kblomqvist/cativity/sw/nrf51/documentation/s110/html/app_fifo_initialized.png

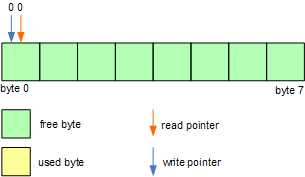
sw/nrf51/documentation/s110/html/app_fifo_initialized.png
