kblomqvist/cativity/sw/nrf51/documentation/s110/html/app_gpiote_01.png

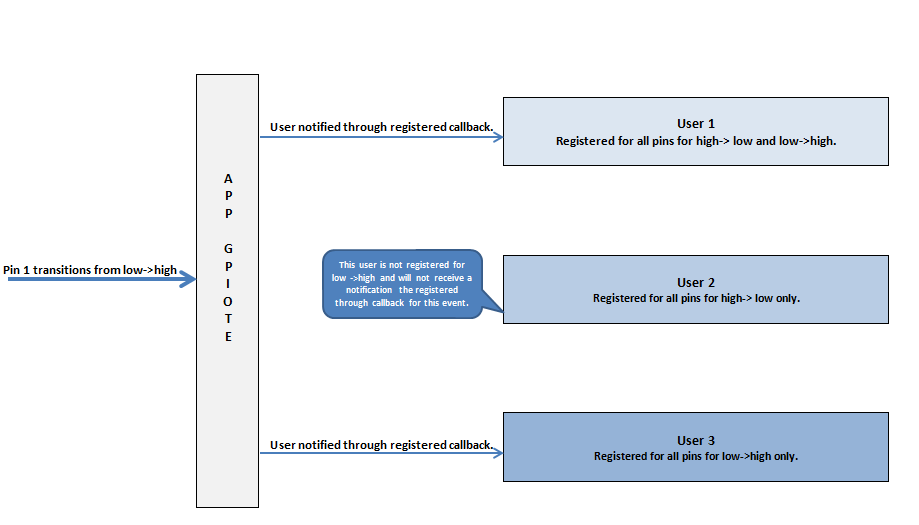
sw/nrf51/documentation/s110/html/app_gpiote_01.png
