kblomqvist/cativity/sw/nrf51/documentation/s110/html/battery_timer_without_scheduler.jpg

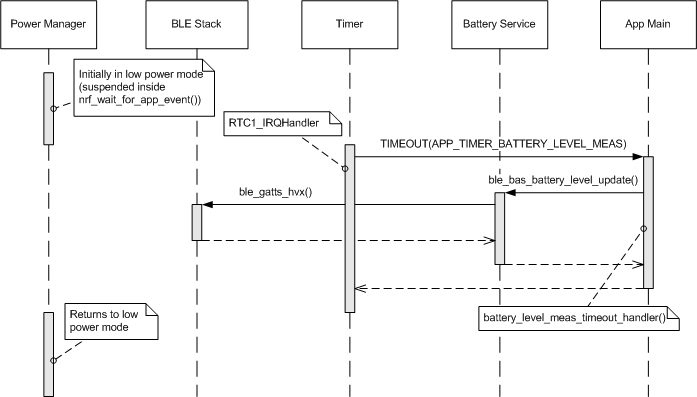
sw/nrf51/documentation/s110/html/battery_timer_without_scheduler.jpg
