kblomqvist/cativity/sw/nrf51/documentation/s110/html/ble_event_without_scheduler.jpg

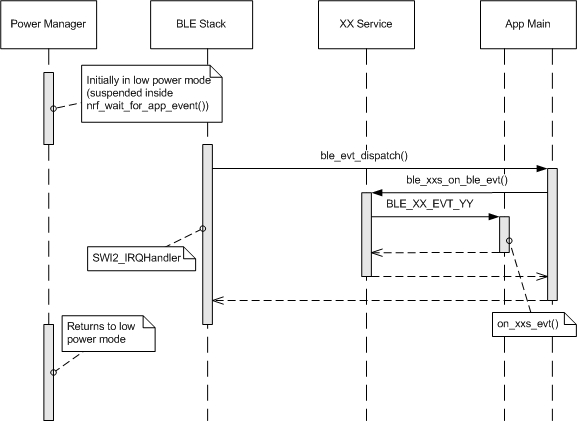
sw/nrf51/documentation/s110/html/ble_event_without_scheduler.jpg
