kblomqvist/cativity/sw/nrf51/documentation/s110/html/blinky_rtx.jpg

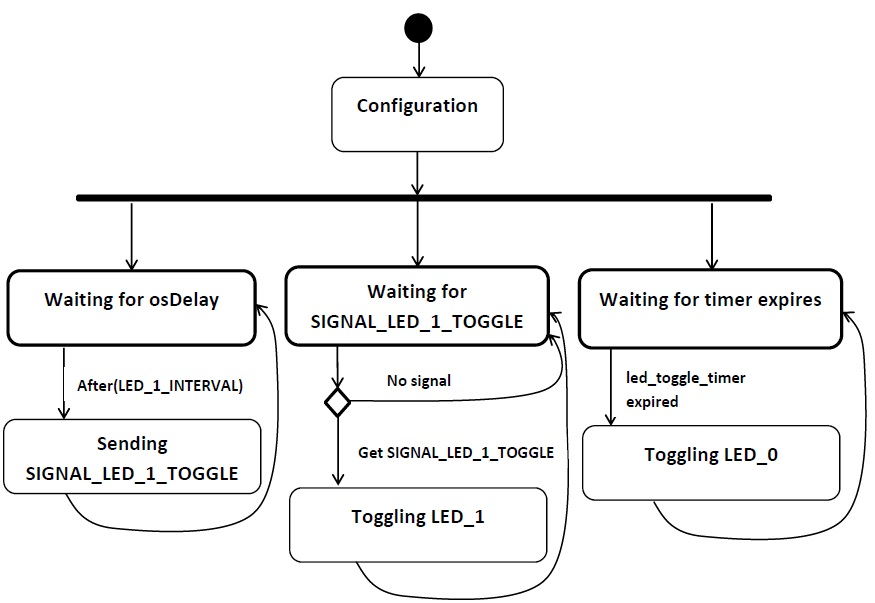
sw/nrf51/documentation/s110/html/blinky_rtx.jpg
