kblomqvist/cativity/sw/nrf51/documentation/s110/html/DTM_DUT.png

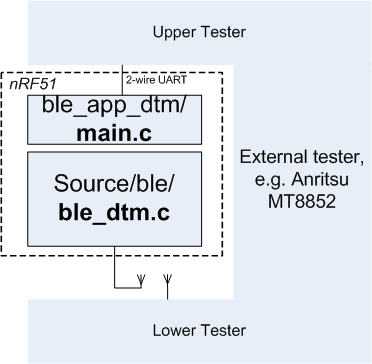
sw/nrf51/documentation/s110/html/DTM_DUT.png
