kblomqvist/cativity/sw/nrf51/documentation/s110/html/dtm_engine.jpg

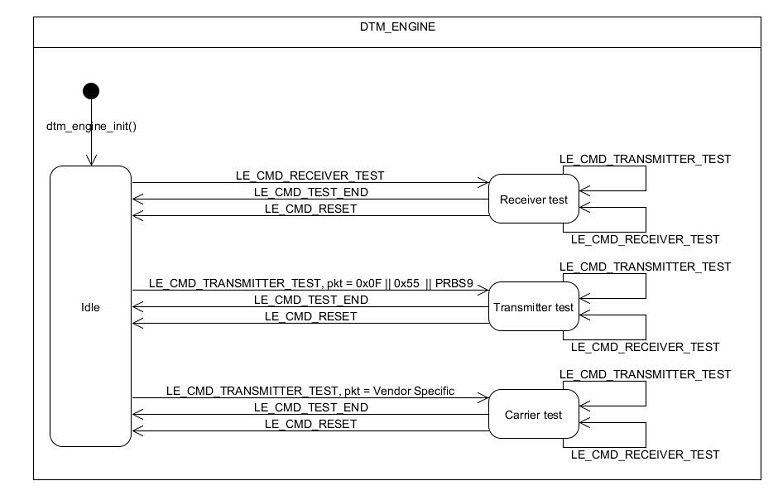
sw/nrf51/documentation/s110/html/dtm_engine.jpg
