kblomqvist/cativity/sw/nrf51/documentation/s110/html/esb_fig1_star_network.png

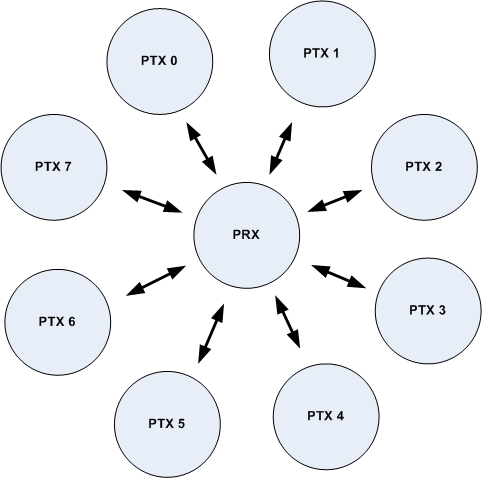
sw/nrf51/documentation/s110/html/esb_fig1_star_network.png
