kblomqvist/cativity/sw/nrf51/documentation/s110/html/esb_fig2_ptx_trans_ok.png

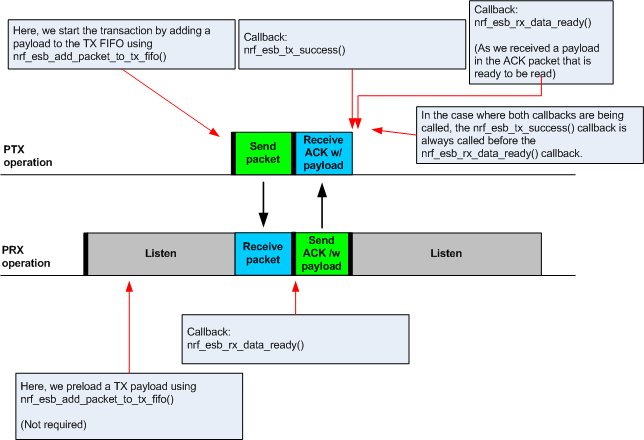
sw/nrf51/documentation/s110/html/esb_fig2_ptx_trans_ok.png
