kblomqvist/cativity/sw/nrf51/documentation/s110/html/esb_fig3_prx_ptx_trans_fail.png

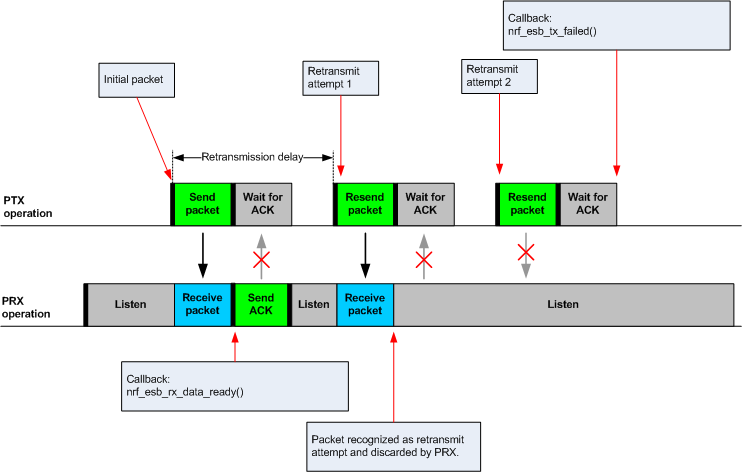
sw/nrf51/documentation/s110/html/esb_fig3_prx_ptx_trans_fail.png
