kblomqvist/cativity/sw/nrf51/documentation/s110/html/exp_dfu_ctrl_pt.png

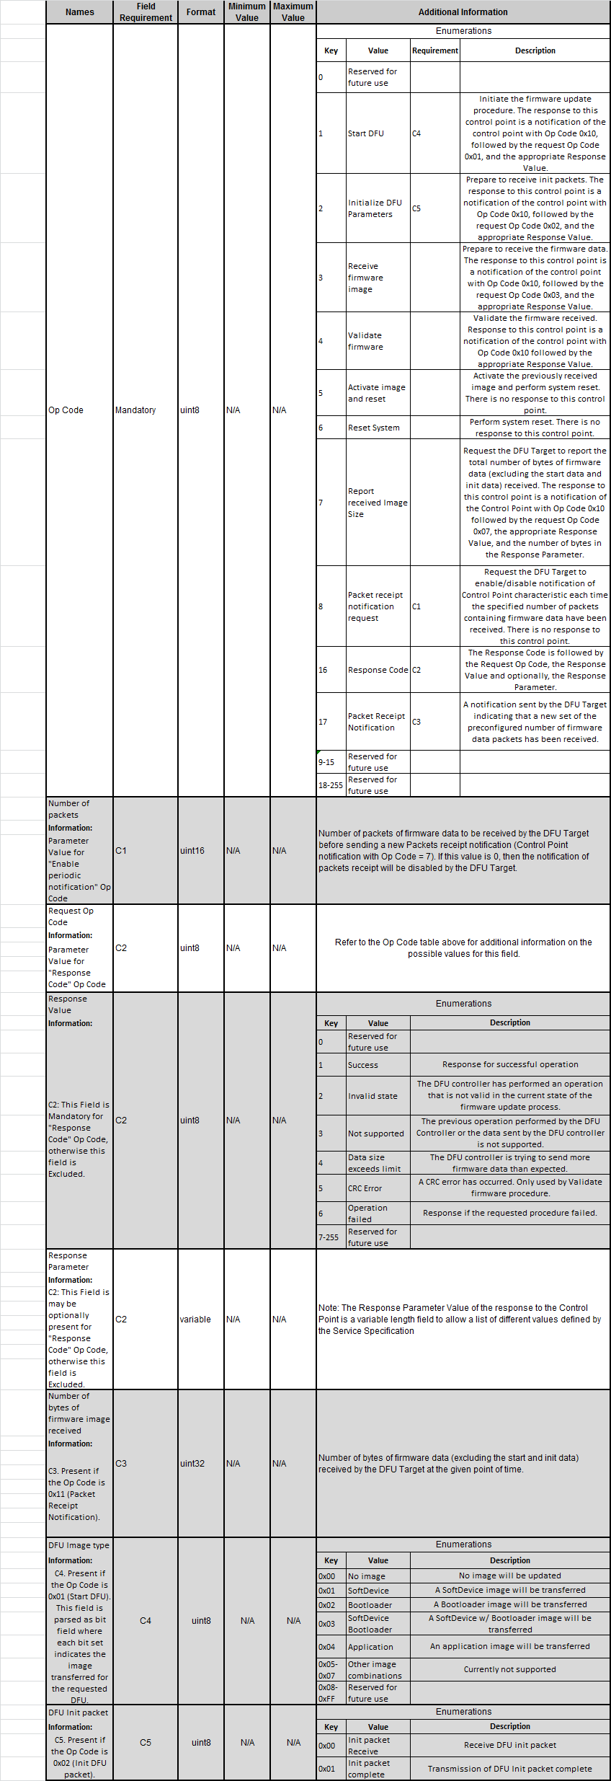
sw/nrf51/documentation/s110/html/exp_dfu_ctrl_pt.png
