kblomqvist/cativity/sw/nrf51/documentation/s110/html/exp_dfu_ota_link_loss.png

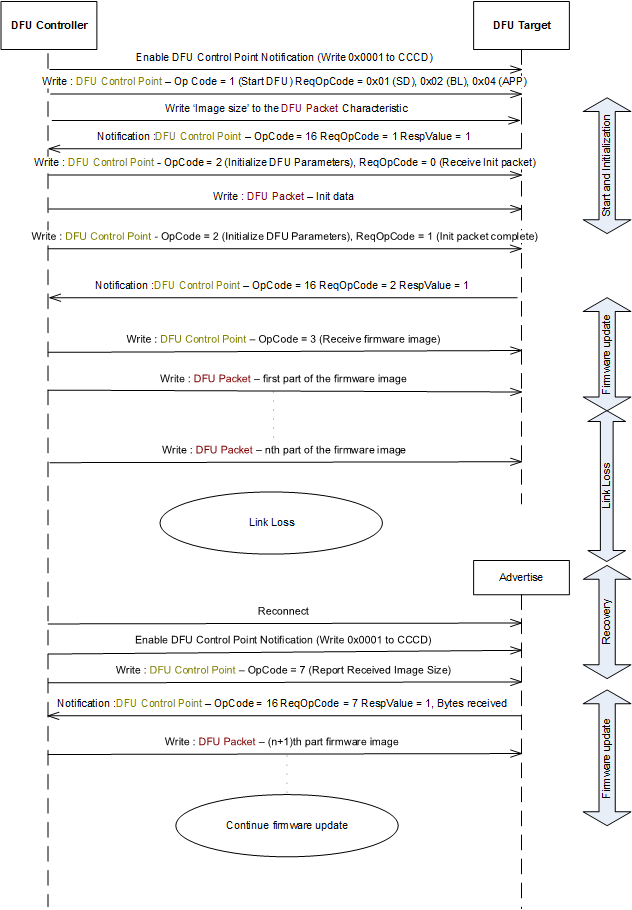
sw/nrf51/documentation/s110/html/exp_dfu_ota_link_loss.png
