kblomqvist/cativity/sw/nrf51/documentation/s110/html/exp_dfu_ota_pkt_rcpt_notif_procedure.png

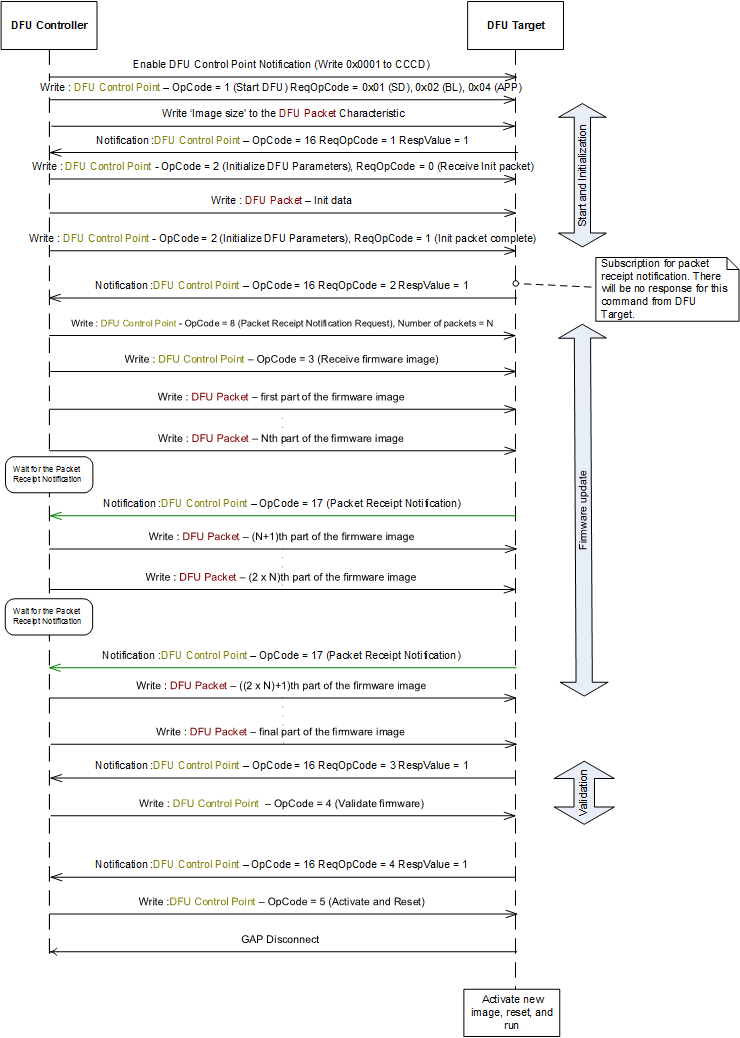
sw/nrf51/documentation/s110/html/exp_dfu_ota_pkt_rcpt_notif_procedure.png
