kblomqvist/cativity/sw/nrf51/documentation/s110/html/exp_ota_dfu_transfer.png

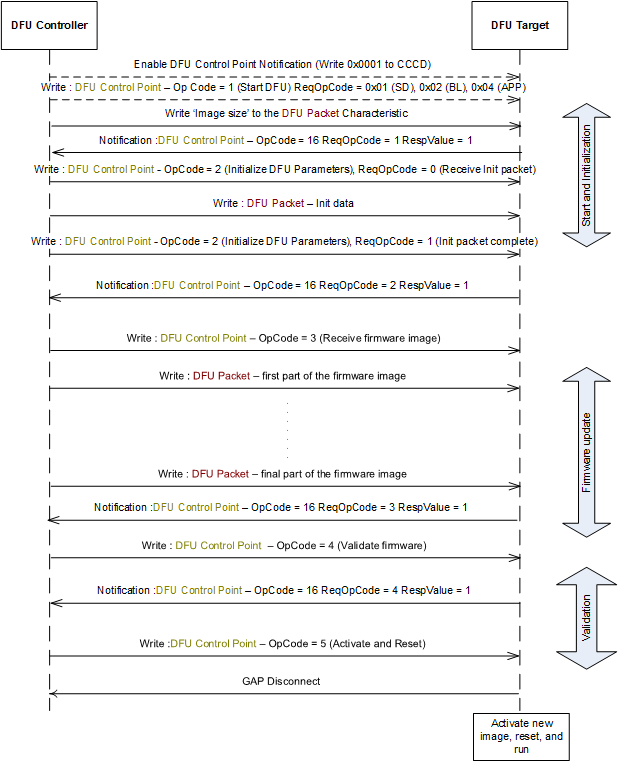
sw/nrf51/documentation/s110/html/exp_ota_dfu_transfer.png
