kblomqvist/cativity/sw/nrf51/documentation/s110/html/gzll_fig2_device_heartbeat.png

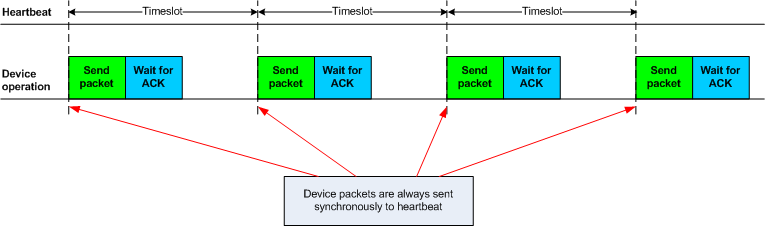
sw/nrf51/documentation/s110/html/gzll_fig2_device_heartbeat.png
