kblomqvist/cativity/sw/nrf51/documentation/s110/html/gzll_fig3_host_heartbeat.png

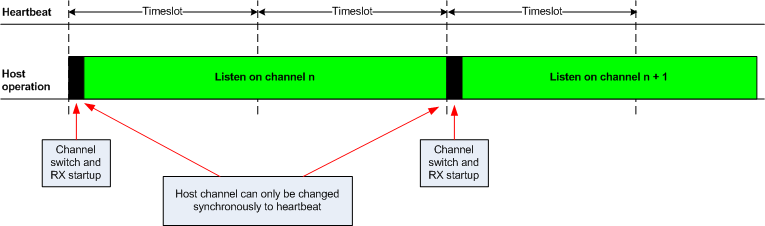
sw/nrf51/documentation/s110/html/gzll_fig3_host_heartbeat.png
