kblomqvist/cativity/sw/nrf51/documentation/s110/html/gzll_fig4_device_channel_switch.png

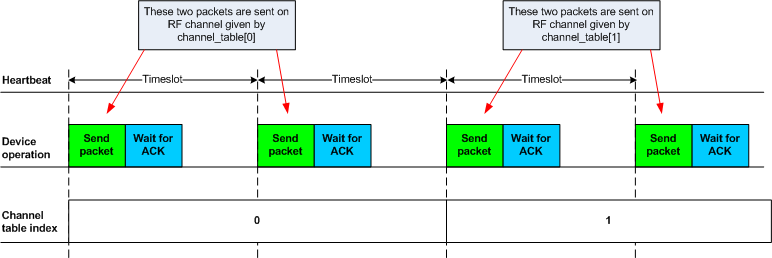
sw/nrf51/documentation/s110/html/gzll_fig4_device_channel_switch.png
