kblomqvist/cativity/sw/nrf51/documentation/s110/html/gzll_fig8_host_dev_trans_fail.png

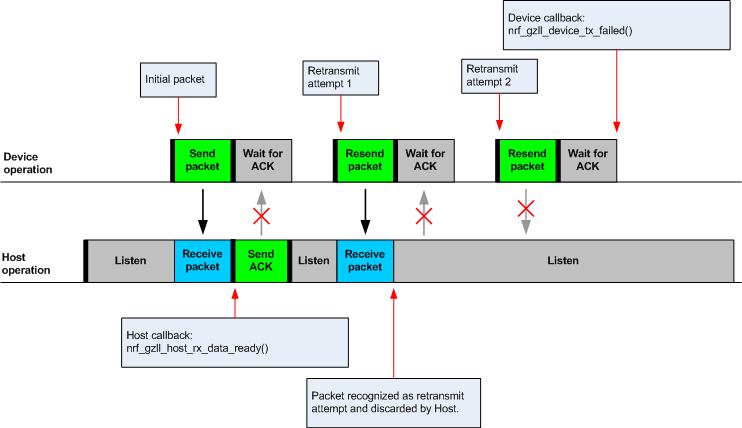
sw/nrf51/documentation/s110/html/gzll_fig8_host_dev_trans_fail.png
