kblomqvist/cativity/sw/nrf51/documentation/s110/html/gzll_fig9_gzll_config_example.png

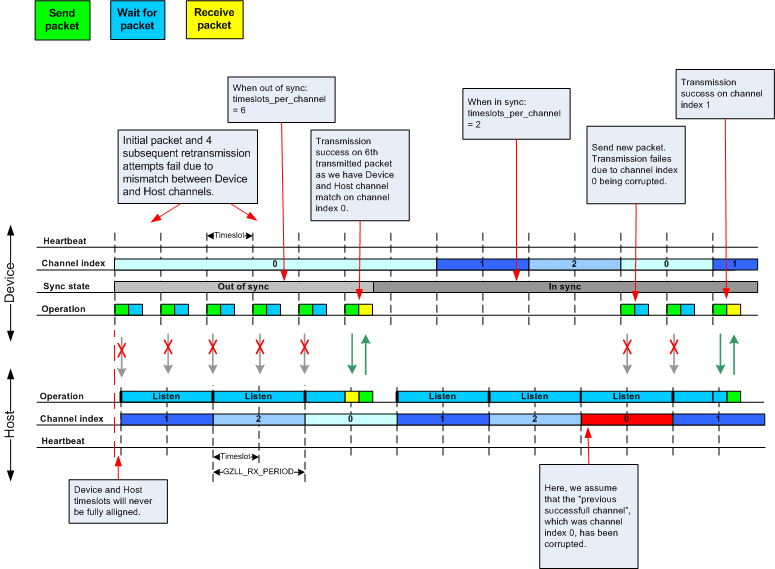
sw/nrf51/documentation/s110/html/gzll_fig9_gzll_config_example.png
