kblomqvist/cativity/sw/nrf51/documentation/s110/html/gzp_factory_defaults.png

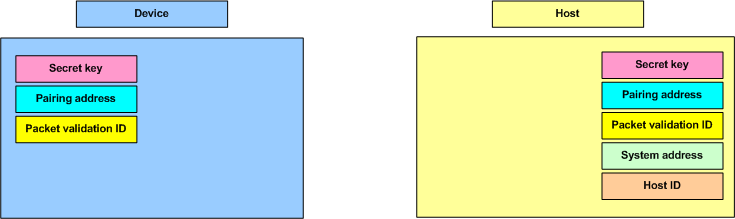
sw/nrf51/documentation/s110/html/gzp_factory_defaults.png
