kblomqvist/cativity/sw/nrf51/documentation/s110/html/gzp_host_id_exchange.png

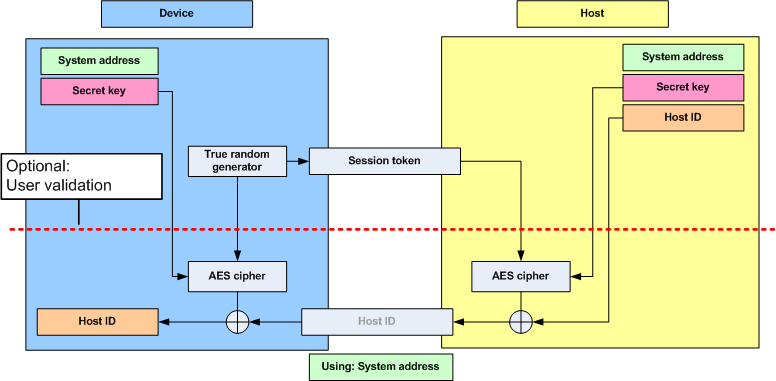
sw/nrf51/documentation/s110/html/gzp_host_id_exchange.png
