kblomqvist/cativity/sw/nrf51/documentation/s110/html/gzp_key_exchange.png

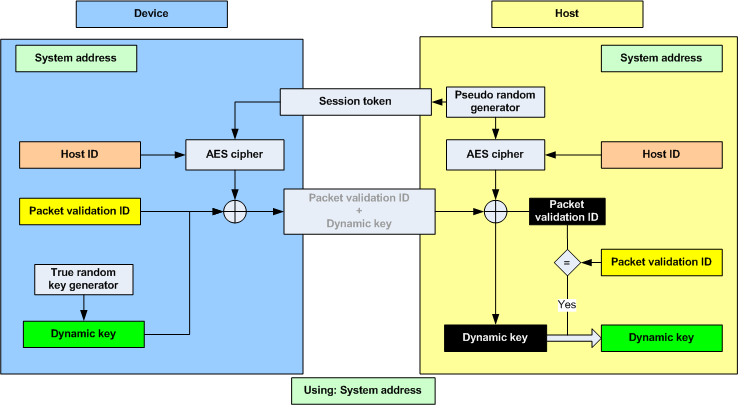
sw/nrf51/documentation/s110/html/gzp_key_exchange.png
