kblomqvist/cativity/sw/nrf51/documentation/s110/html/gzp_user_data_exchange.png

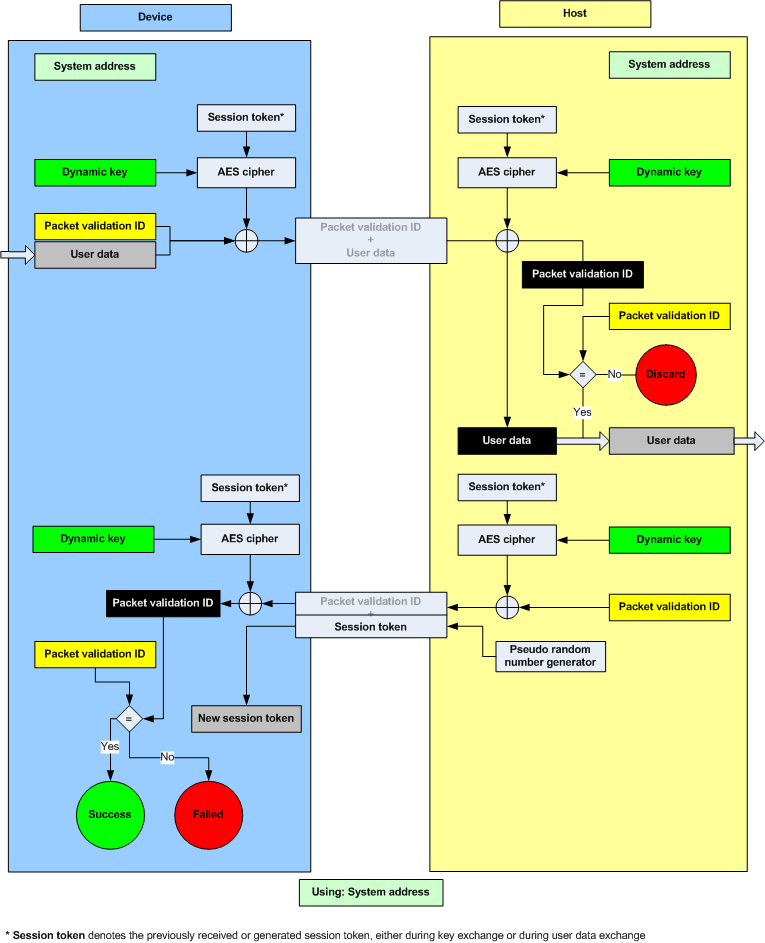
sw/nrf51/documentation/s110/html/gzp_user_data_exchange.png
