kblomqvist/cativity/sw/nrf51/documentation/s110/html/hci_transport_tx_sm.png

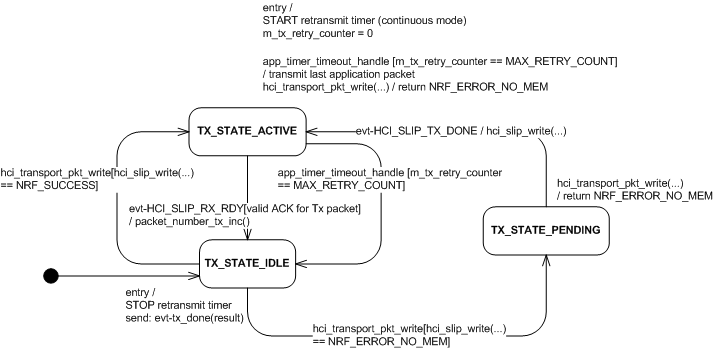
sw/nrf51/documentation/s110/html/hci_transport_tx_sm.png
