kblomqvist/cativity/sw/nrf51/documentation/s110/html/keil_project_bootloader_location.png

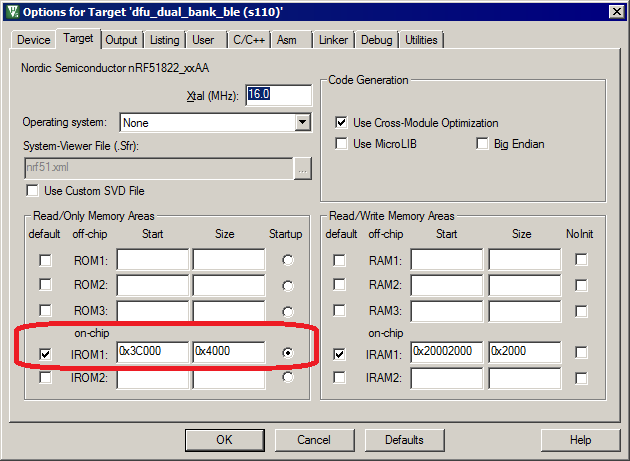
sw/nrf51/documentation/s110/html/keil_project_bootloader_location.png
