kblomqvist/cativity/sw/nrf51/documentation/s110/html/keil_project_flash_tool.png

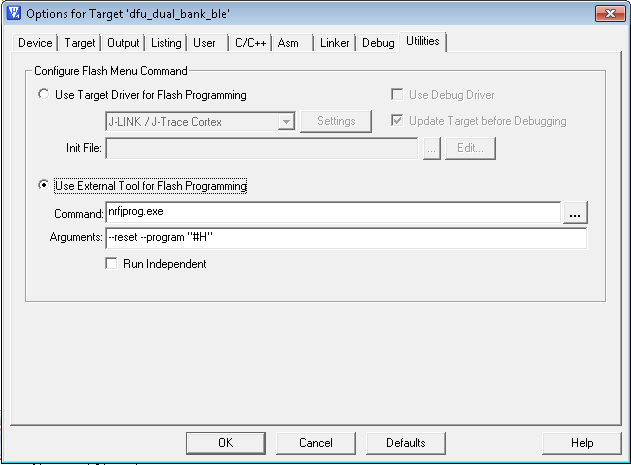
sw/nrf51/documentation/s110/html/keil_project_flash_tool.png
