kblomqvist/cativity/sw/nrf51/documentation/s110/html/msc_inline_mscgraph_12.png

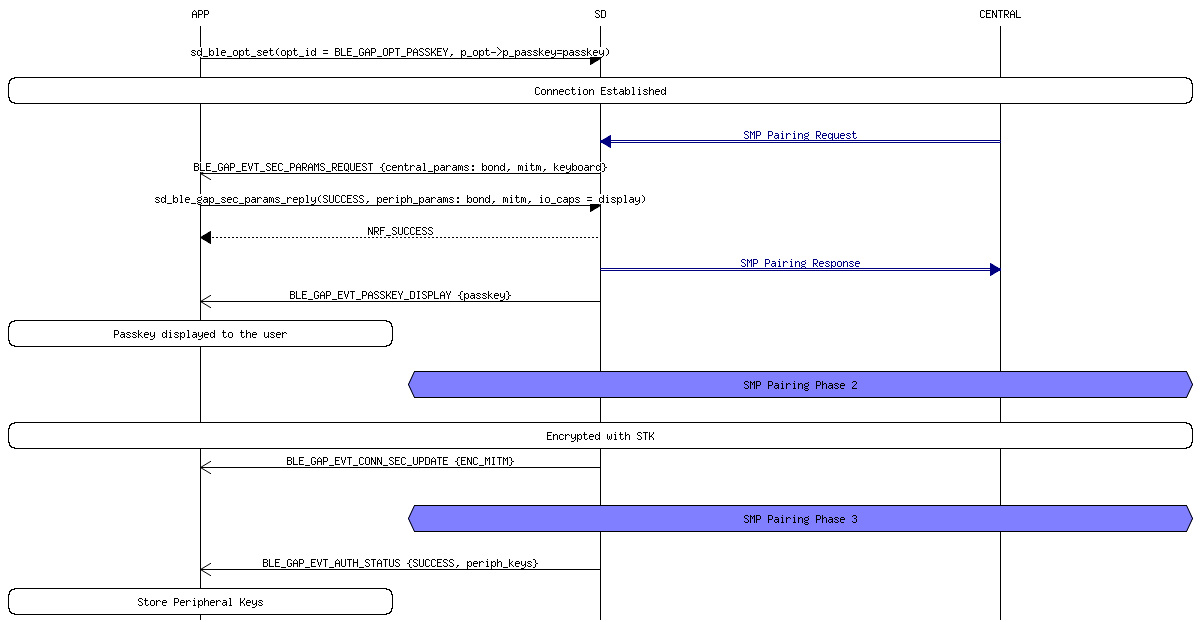
sw/nrf51/documentation/s110/html/msc_inline_mscgraph_12.png
