kblomqvist/cativity/sw/nrf51/documentation/s110/html/msc_inline_mscgraph_41.png

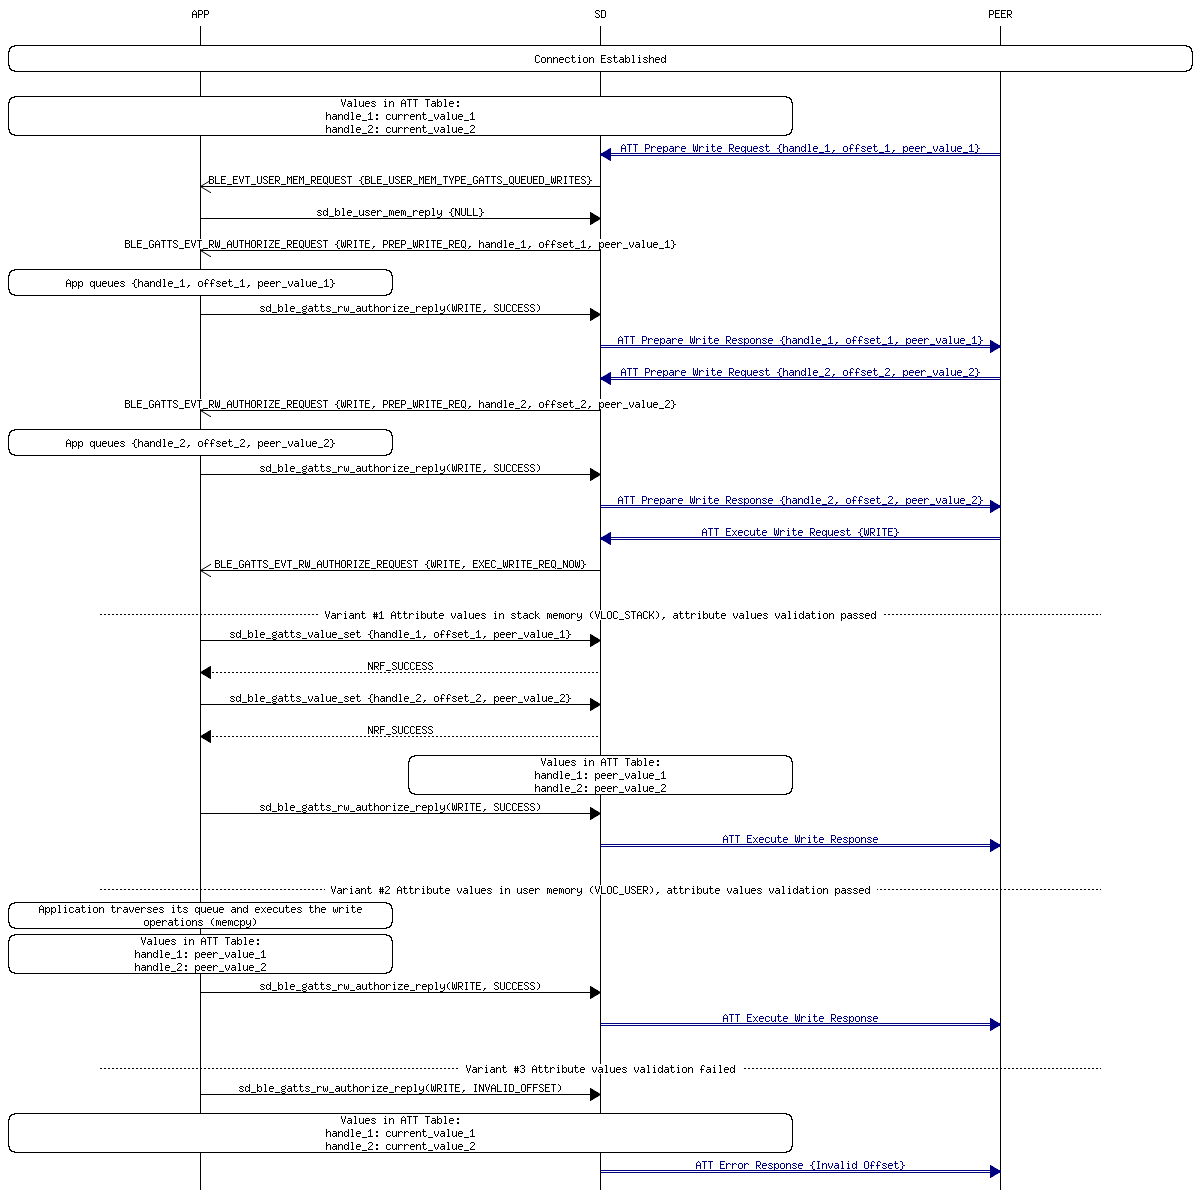
sw/nrf51/documentation/s110/html/msc_inline_mscgraph_41.png
