kblomqvist/cativity/sw/nrf51/documentation/s110/html/msc_inline_mscgraph_53.png

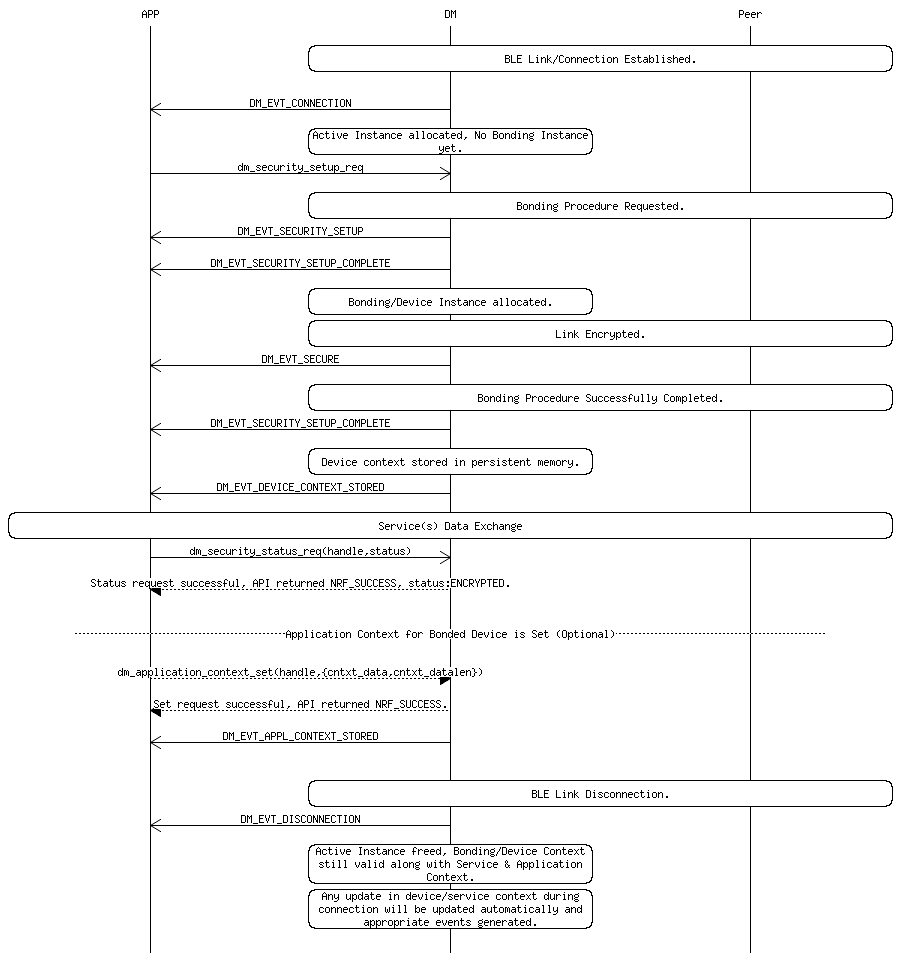
sw/nrf51/documentation/s110/html/msc_inline_mscgraph_53.png
