kblomqvist/cativity/sw/nrf51/documentation/s110/html/ota_dfu_buttonless.png

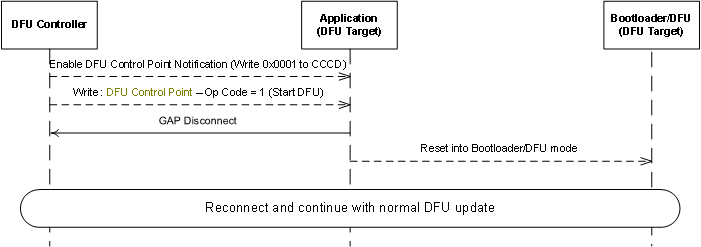
sw/nrf51/documentation/s110/html/ota_dfu_buttonless.png
