kblomqvist/cativity/sw/nrf51/documentation/s110/html/ota_dfu_typical_ctrl_pt_procedure.png

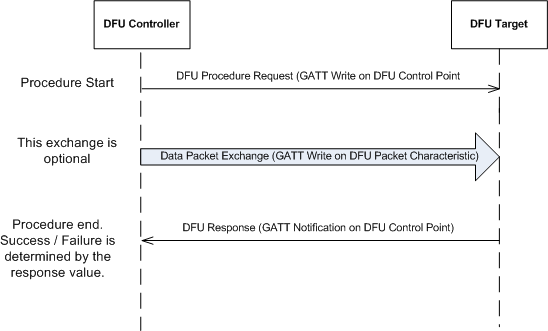
sw/nrf51/documentation/s110/html/ota_dfu_typical_ctrl_pt_procedure.png
