kblomqvist/cativity/sw/nrf51/documentation/s110/html/pstorage.png

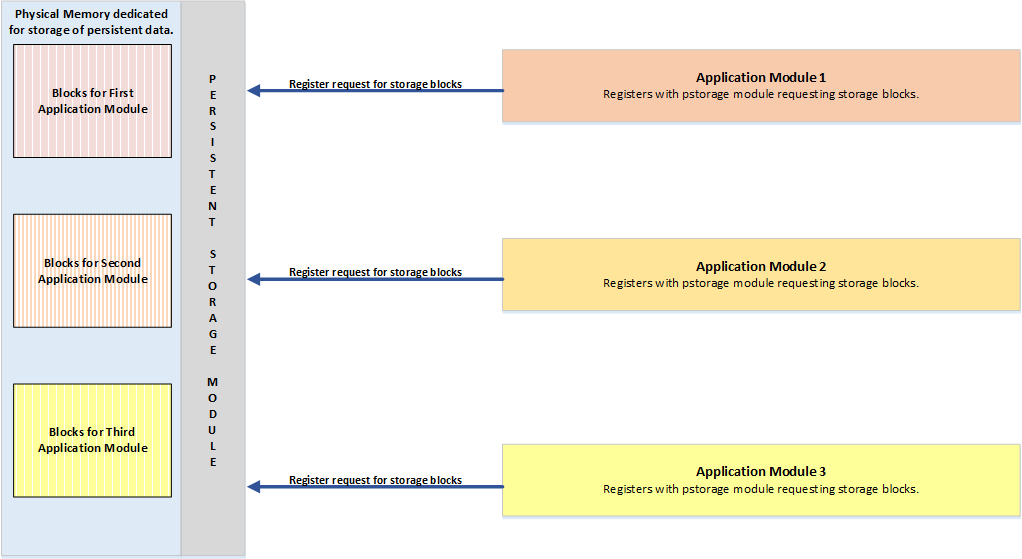
sw/nrf51/documentation/s110/html/pstorage.png
