kblomqvist/cativity/sw/nrf51/documentation/s110/html/scheduler_working.jpg

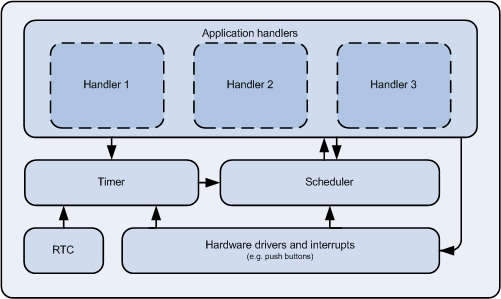
sw/nrf51/documentation/s110/html/scheduler_working.jpg
