kblomqvist/cativity/sw/nrf51/documentation/s110/html/spi_slave_driver_sm.png

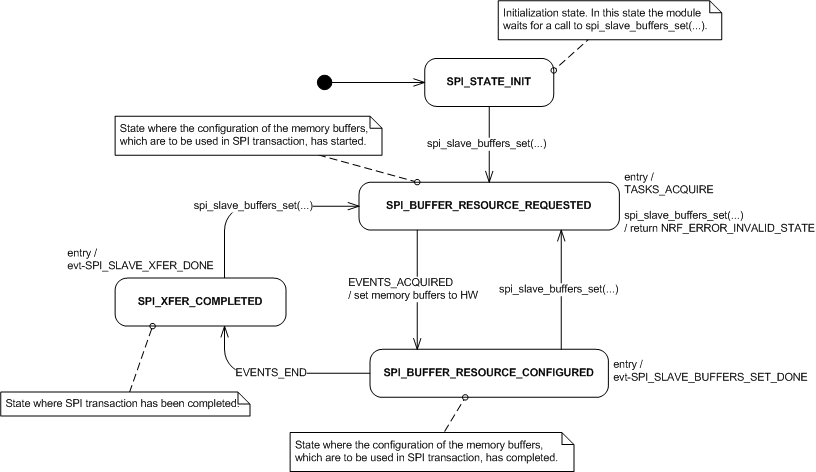
sw/nrf51/documentation/s110/html/spi_slave_driver_sm.png
