kblomqvist/cativity/sw/nrf51/documentation/s110/html/timer_example_sm.png

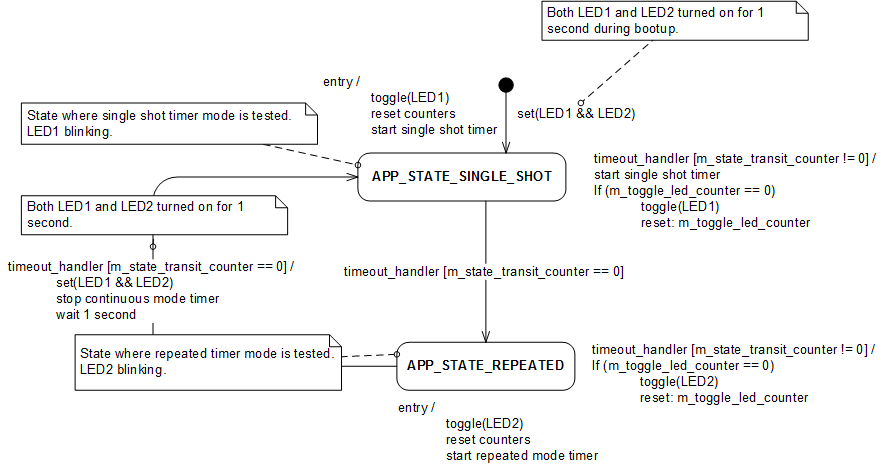
sw/nrf51/documentation/s110/html/timer_example_sm.png
