kblomqvist/cativity/sw/nrf51/documentation/s110/html/uart_state_machine_tx_no_flow_control.png

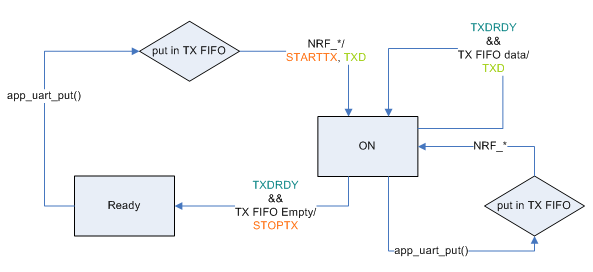
sw/nrf51/documentation/s110/html/uart_state_machine_tx_no_flow_control.png
