kblomqvist/cativity/sw/nrf51/documentation/s110/html/uart_state_machine_tx_with_flow_control.png

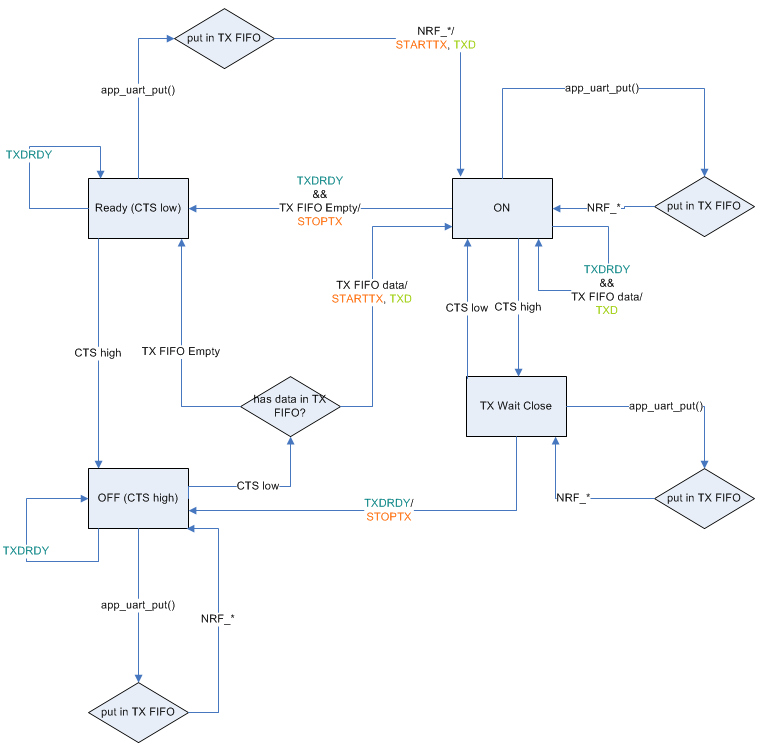
sw/nrf51/documentation/s110/html/uart_state_machine_tx_with_flow_control.png
