kblomqvist/cativity/sw/nrf51/documentation/s110/html/uicr_example_ant_aa.png

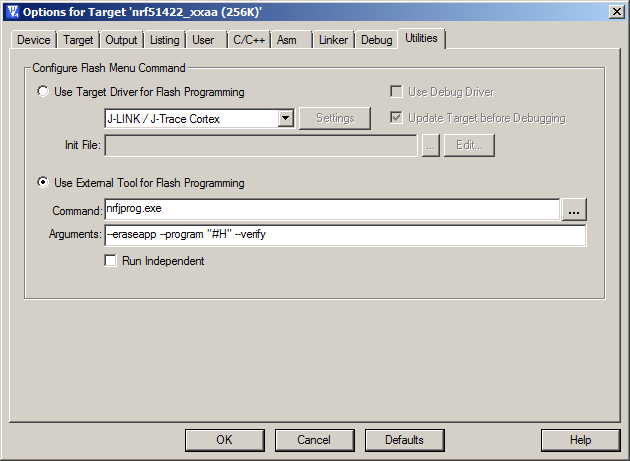
sw/nrf51/documentation/s110/html/uicr_example_ant_aa.png
