kblomqvist/cativity/sw/nrf51/documentation/s120/html/ble_event_with_scheduler.jpg

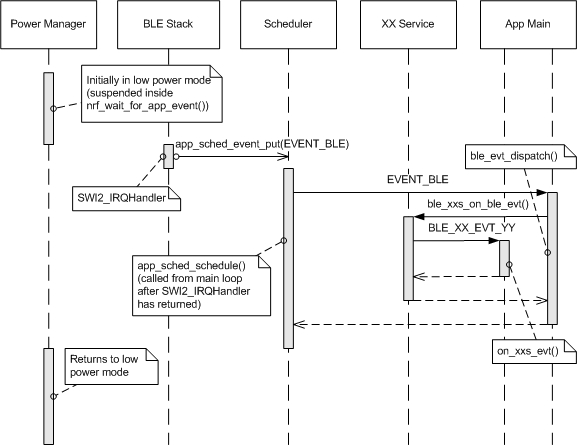
sw/nrf51/documentation/s120/html/ble_event_with_scheduler.jpg
