kblomqvist/cativity/sw/nrf51/documentation/s120/html/memory_pool.png

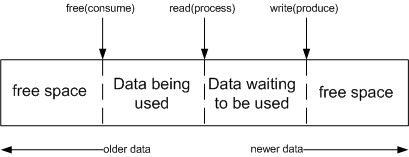
sw/nrf51/documentation/s120/html/memory_pool.png
