kblomqvist/cativity/sw/nrf51/documentation/s120/html/msc_inline_mscgraph_6.png

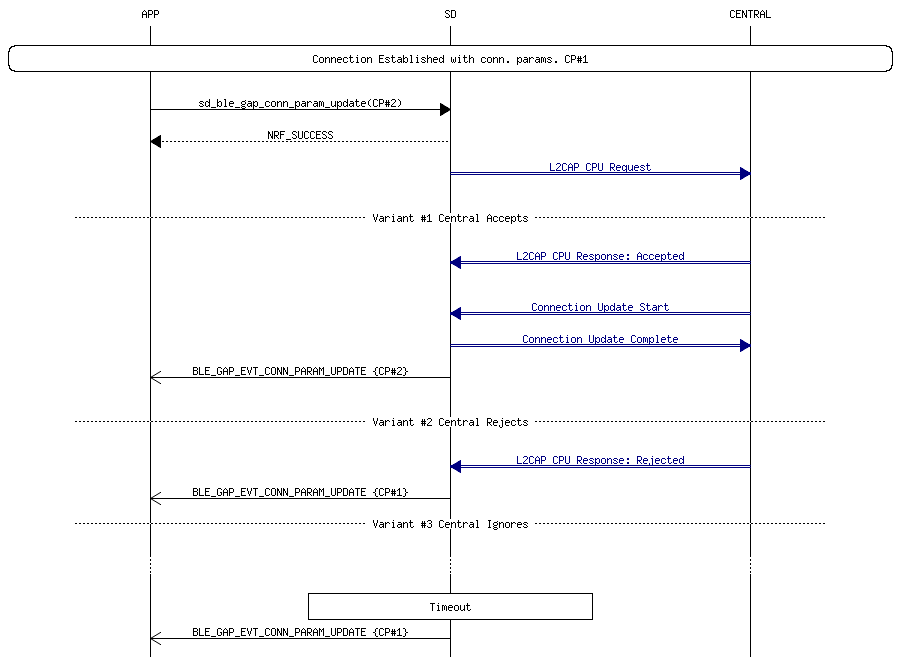
sw/nrf51/documentation/s120/html/msc_inline_mscgraph_6.png
