kblomqvist/cativity/sw/nrf51/documentation/s120/html/msc_inline_mscgraph_14.png

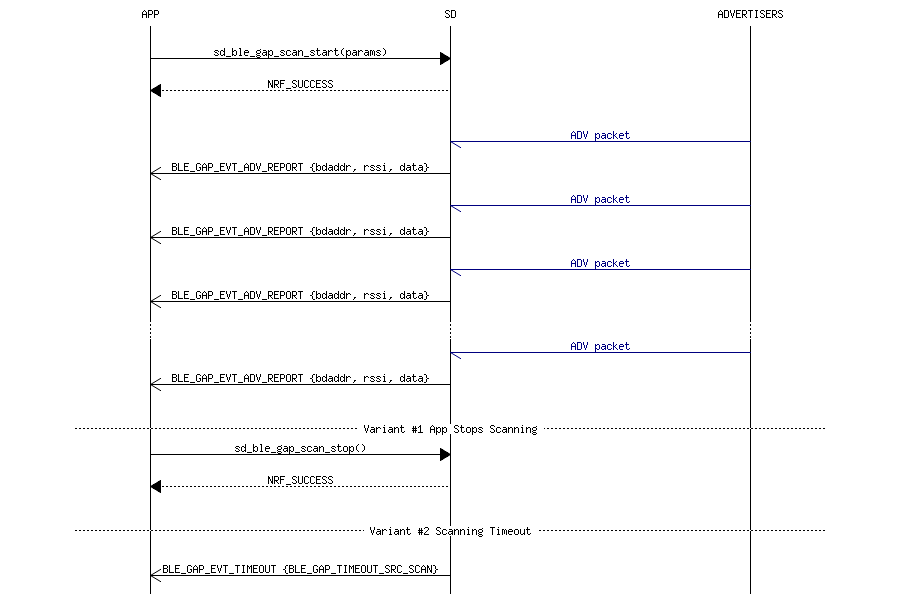
sw/nrf51/documentation/s120/html/msc_inline_mscgraph_14.png
