kblomqvist/cativity/sw/nrf51/documentation/s120/html/msc_inline_mscgraph_26.png

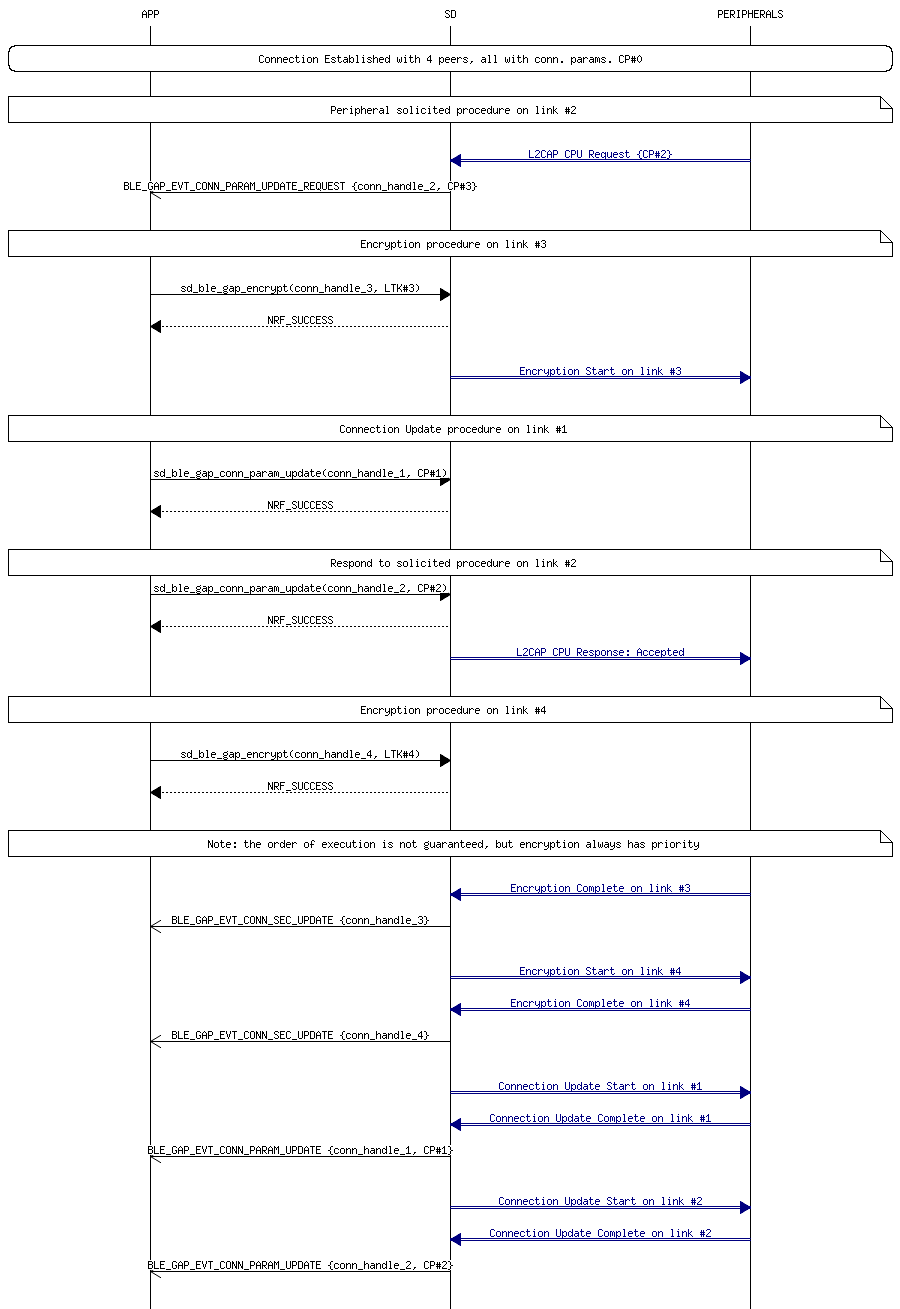
sw/nrf51/documentation/s120/html/msc_inline_mscgraph_26.png
