kblomqvist/cativity/sw/nrf51/documentation/s120/html/ppi_example.png

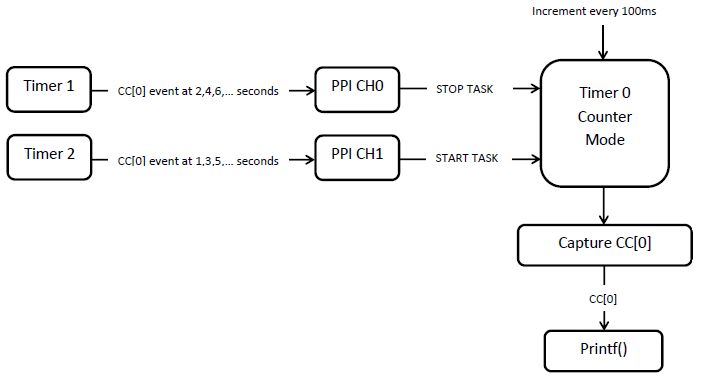
sw/nrf51/documentation/s120/html/ppi_example.png
