kblomqvist/cativity/sw/nrf51/documentation/s210/html/ant_dfu_screen.jpg

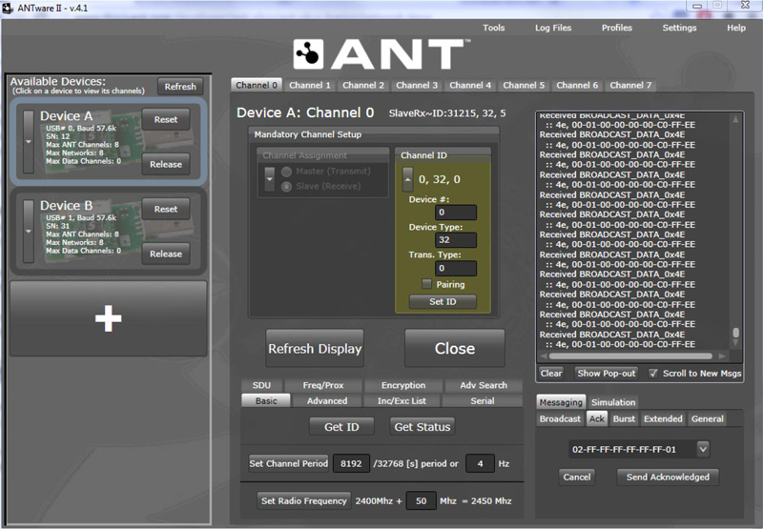
sw/nrf51/documentation/s210/html/ant_dfu_screen.jpg
