kblomqvist/cativity/sw/nrf51/documentation/s210/html/sdm_tx_flowchart.png

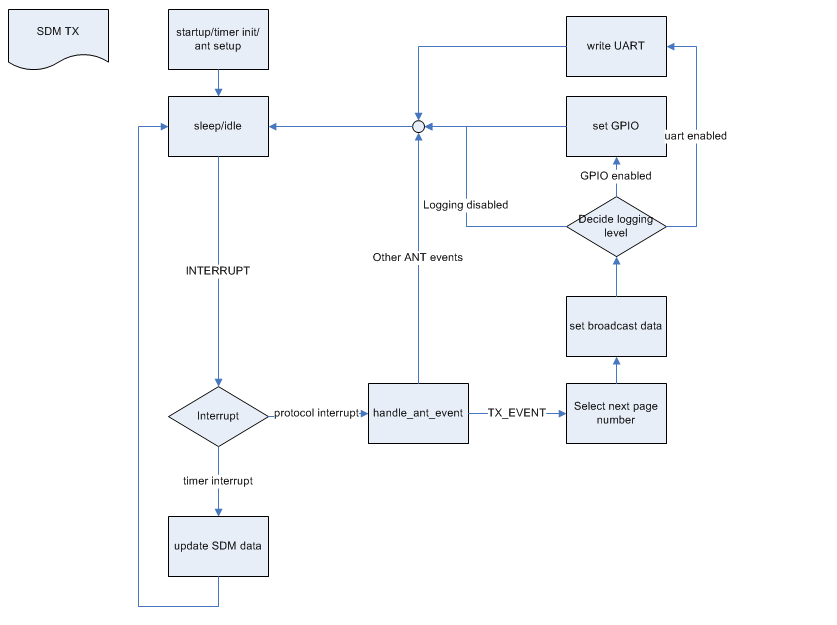
sw/nrf51/documentation/s210/html/sdm_tx_flowchart.png
