kblomqvist/cativity/sw/nrf51/documentation/s210/html/bicycle_power_rx_calibration_sm.png

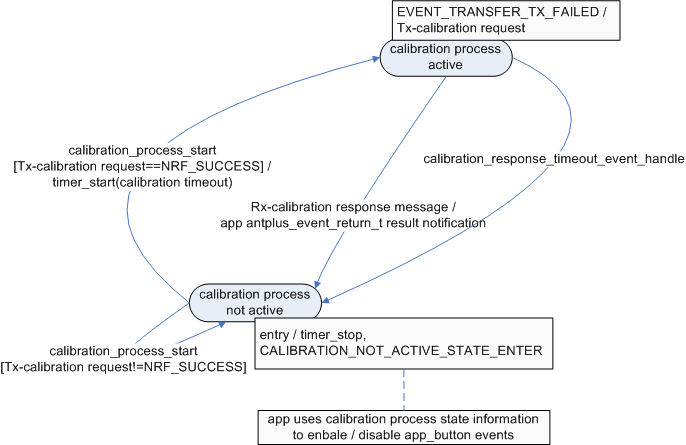
sw/nrf51/documentation/s210/html/bicycle_power_rx_calibration_sm.png
