kblomqvist/cativity/hw/kicad/nrf-v1.pdf

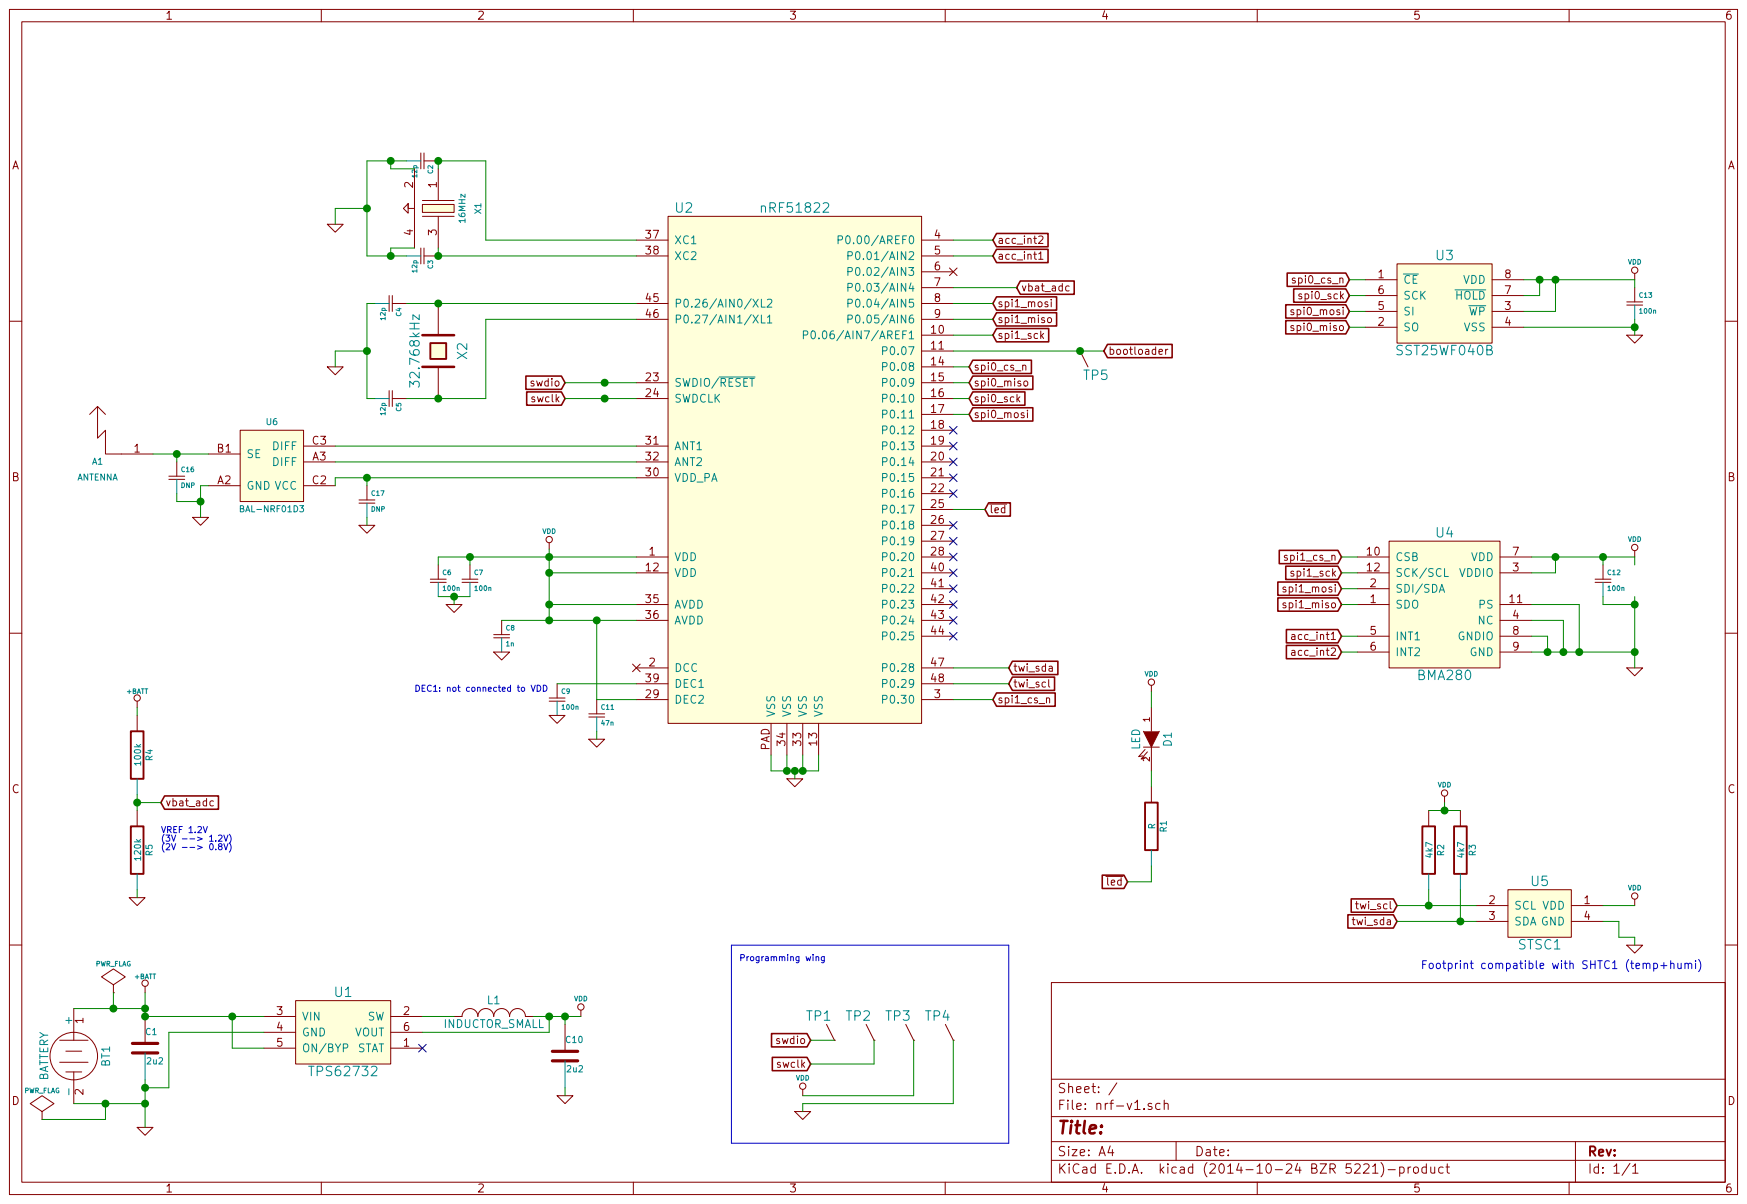
[picture p111: page 1]
